g8keeperzuul/Chime/content/3d-model/art-deco-chime-enclosure-model-2.png

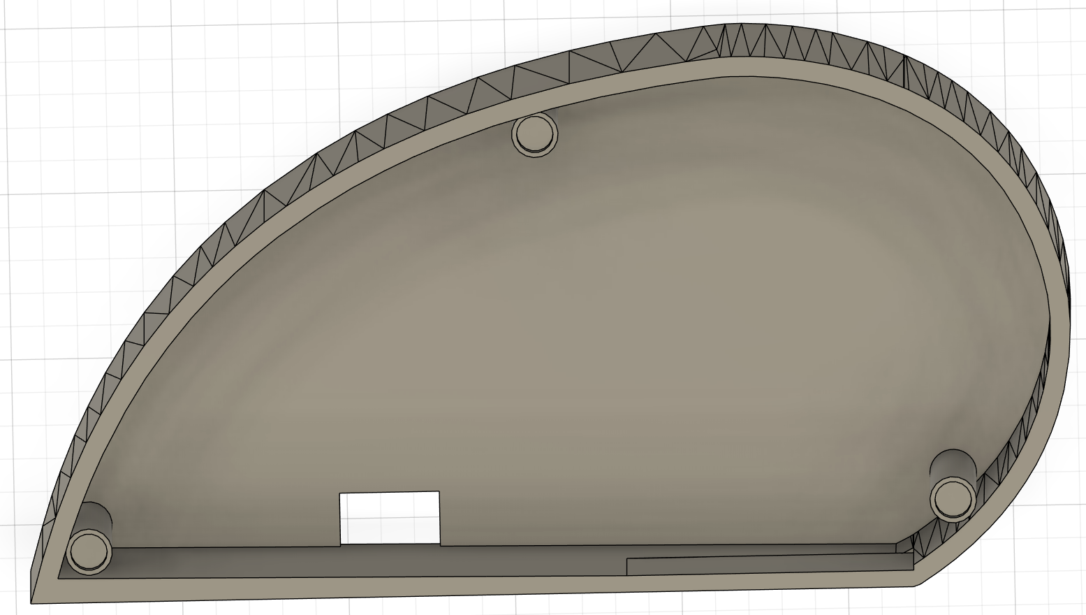
content/3d-model/art-deco-chime-enclosure-model-2.png
