g8keeperzuul/Chime/content/3d-model/art-deco-chime-enclosure-model.png

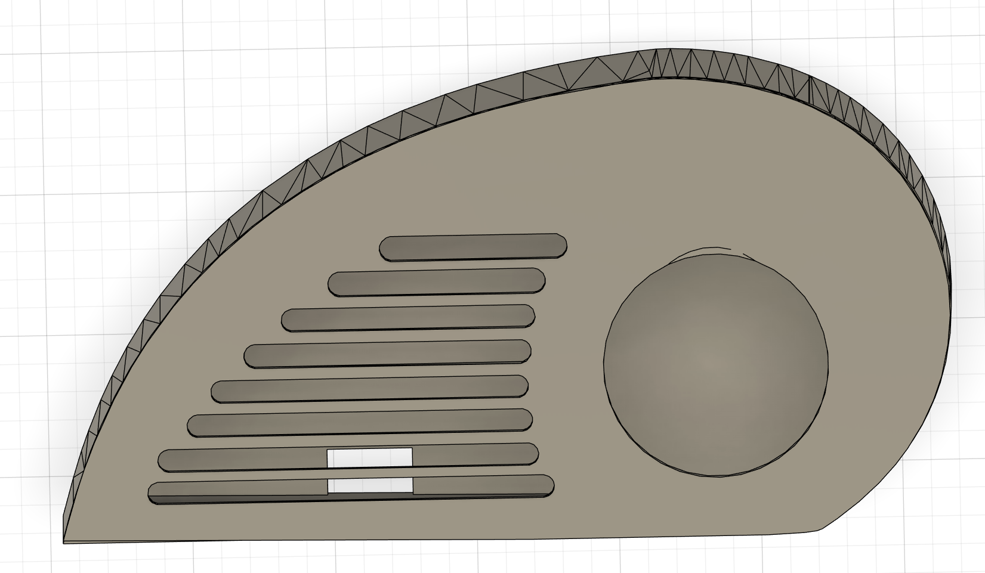
content/3d-model/art-deco-chime-enclosure-model.png
