g8keeperzuul/Chime/include/graphics.h

#ifndef GRAPHICS_H
#define GRAPHICS_H

#include <Arduino.h> // for PROGMEM

// *********************************************************************************************************************
// Note: 'convert' is from ImageMagick
// Remove transparent background. Replace with white.
// $ convert fire-transparent-bg.png -background white -flatten fire.png

// Resize image. Max screen size is 128x128.
// $ convert -resize 128x128 fire.png fire128.png

// Invert image; swap colors.
// $ convert fire128.png +level-colors white,black fire128inv.png

// Generate binary array.
// $ convert fire128.png XBM:FIRE.xbm
// OR https://notisrac.github.io/FileToCArray/

static const char* NONE_LABEL = "NONE";               // size 1
static const char* MEDIUM_TEXT_LABEL = "MEDIUM_TEXT"; // size 2 (max 10 chars across, 6 lines)
static const char* LARGE_TEXT_LABEL = "LARGE_TEXT";   // size 3 (max  7 chars across, 5 lines)


static const char* FIRE_LABEL = "FIRE";

#define FIRE_HEIGHT 96
#define FIRE_WIDTH 96

// array size is 1152
static const unsigned char FIRE_BITMAP[] PROGMEM  = {
  B00000000, B00000000, B00000000, B00000000, B00000000, B00000000, B00000000, B00000000, B00000000, B00000000, B00000000, B00000000, 
  B00000000, B00000000, B00000000, B00000000, B00000000, B00000000, B00000000, B00000000, B00000000, B00000000, B00000000, B00000000, 
  B00000000, B00000000, B00000000, B00000000, B00000000, B00000000, B00000000, B00000000, B00000000, B00000000, B00000000, B00000000, 
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
  B00000000, B00000000, B00000011, B11111111, B11111111, B11111111, B11111111, B11000000, B00000000, B11111111, B00000000, B00000000, 
  B00000000, B00000000, B00000111, B11111111, B11111111, B11111111, B11111111, B11100000, B00000000, B11111111, B00000000, B00000000, 
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
};

#endif
